InteractionEngineer/Schuetteldose/OSC.cpp

#include "OSC.h"

OSC::OSC(const char *ssid, const char *pass, const IPAddress &outIp, unsigned int outPort, unsigned int localPort)
  : _ssid(ssid), _pass(pass), _outIp(outIp), _outPort(outPort), _localPort(localPort) {
  _routeState = "/sprayar/microcontroller/state";
  _routePing = "/sprayar/microcontroller/ping";
  _routeCharge = "/sprayar/microcontroller/charge";
  _previousMillis = millis();
}

void OSC::setup(LED *ledInstance) {
  Serial.println();
  Serial.print("Connecting to ");
  Serial.println(_ssid.c_str());
  WiFi.begin(_ssid.c_str(), _pass.c_str());

  unsigned long previousMillis = millis();  // Store the current time
  while (WiFi.status() != WL_CONNECTED) {
    unsigned long currentMillis = millis();
    if (currentMillis - previousMillis >= 500) {
      previousMillis = currentMillis;  // Update the stored time
      Serial.print(".");
      ledInstance->pulse(5, 20);
    }
  }
  Serial.println("");

  Serial.println("WiFi connected");
  Serial.println("IP address: ");
  Serial.println(WiFi.localIP());

  Serial.println("Starting UDP");
  _Udp.begin(_localPort);
  Serial.print("Local port: ");
  Serial.println(_localPort);
}


void OSC::receive(OSCMessage &msg) {

  int size = _Udp.parsePacket();

  if (size > 0) {
    while (size--) {
      msg.fill(_Udp.read());
    }
    if (msg.hasError()) {
      _error = msg.getError();
      Serial.print("error: ");
      Serial.println(_error);
    } else {
      char str[100];
      msg.getString(0, str, 100);
      Serial.println(str);
    }
  }
}

void OSC::send(OSCMessage &msg) {
  _Udp.beginPacket(_outIp, _outPort);
  msg.send(_Udp);
  _Udp.endPacket();
  msg.empty();
}

void OSC::ping() {
  OSCMessage msg(_routePing);
  msg.add("PING");
  send(msg);
}

void OSC::sendCharge(float charge) {
  OSCMessage msg(_routeCharge);
  msg.add(charge);
  send(msg);
}

void OSC::sendState(boolean isGrabbed, int32_t appliedForce) {
  OSCMessage msg(_routeState);
  msg.add(isGrabbed);
  msg.add(appliedForce);
  send(msg);
}
